stamatis-mavitzis/Power-Amplifier/Images/PXL_20261008_083058387.jpg

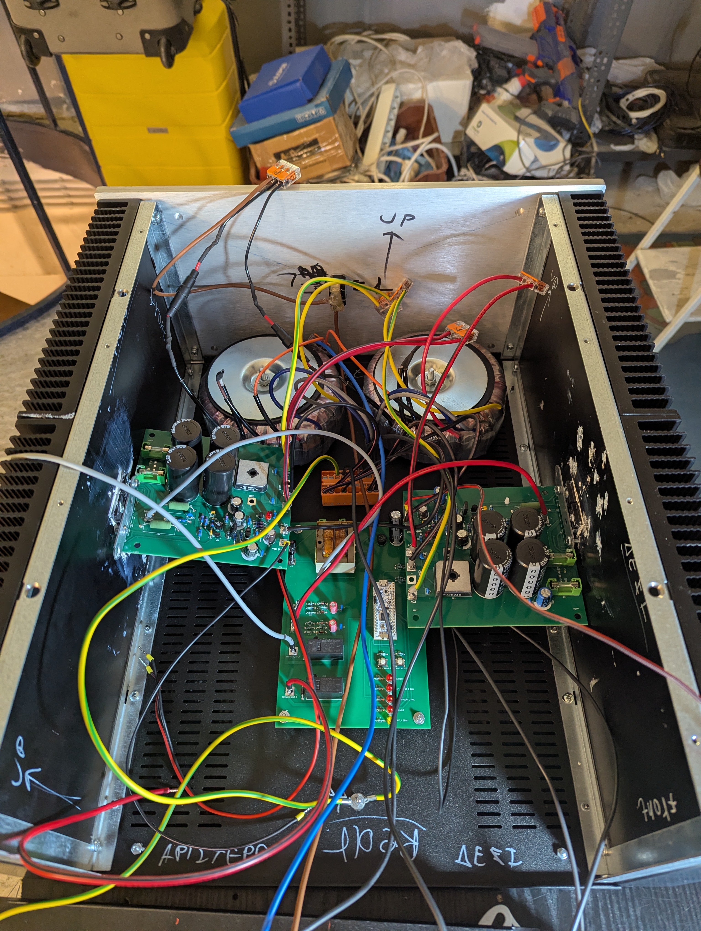
Images/PXL_20261008_083058387.jpg
