stamatis-mavitzis/Power-Amplifier/Images/PXL_20261008_091854718.jpg

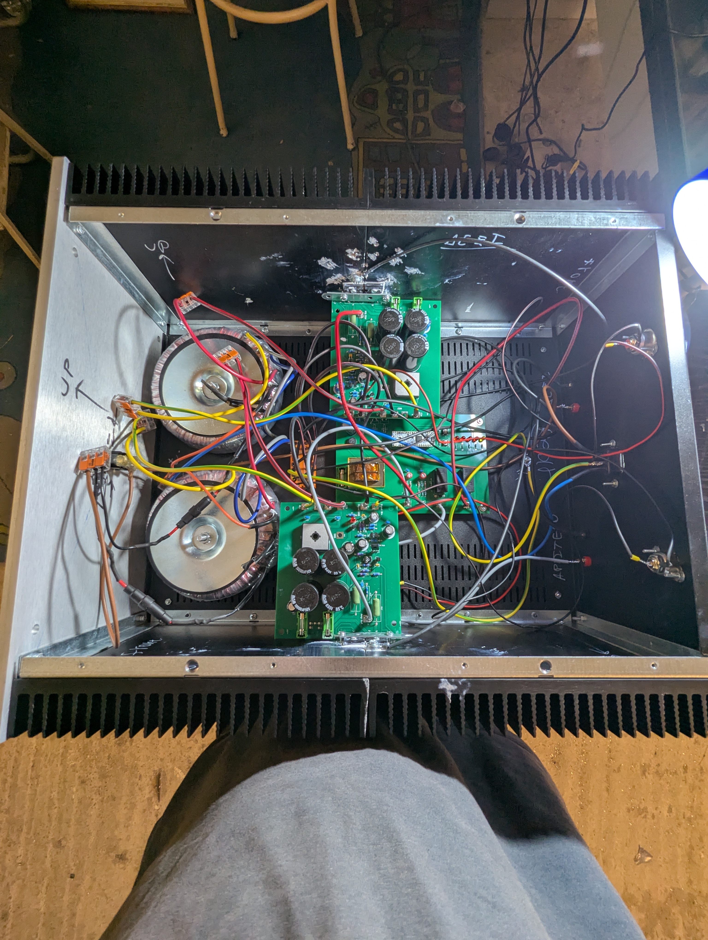
Images/PXL_20261008_091854718.jpg
