stamatis-mavitzis/Power-Amplifier/Images/PXL_20261008_150706582.jpg

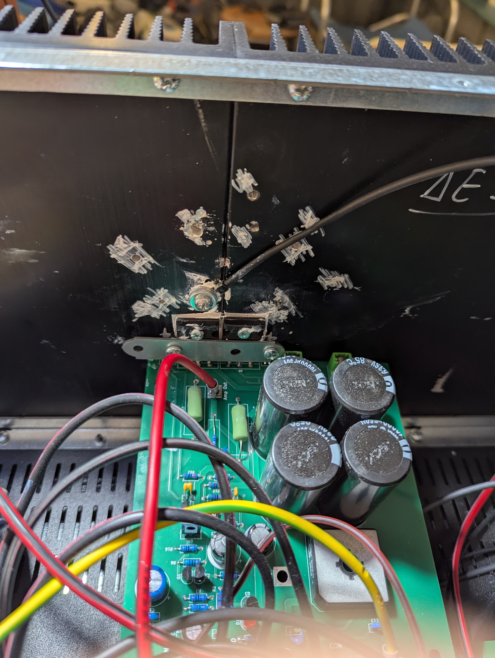
Images/PXL_20261008_150706582.jpg
