stamatis-mavitzis/Power-Amplifier/Images/PXL_20261008_164403830.jpg

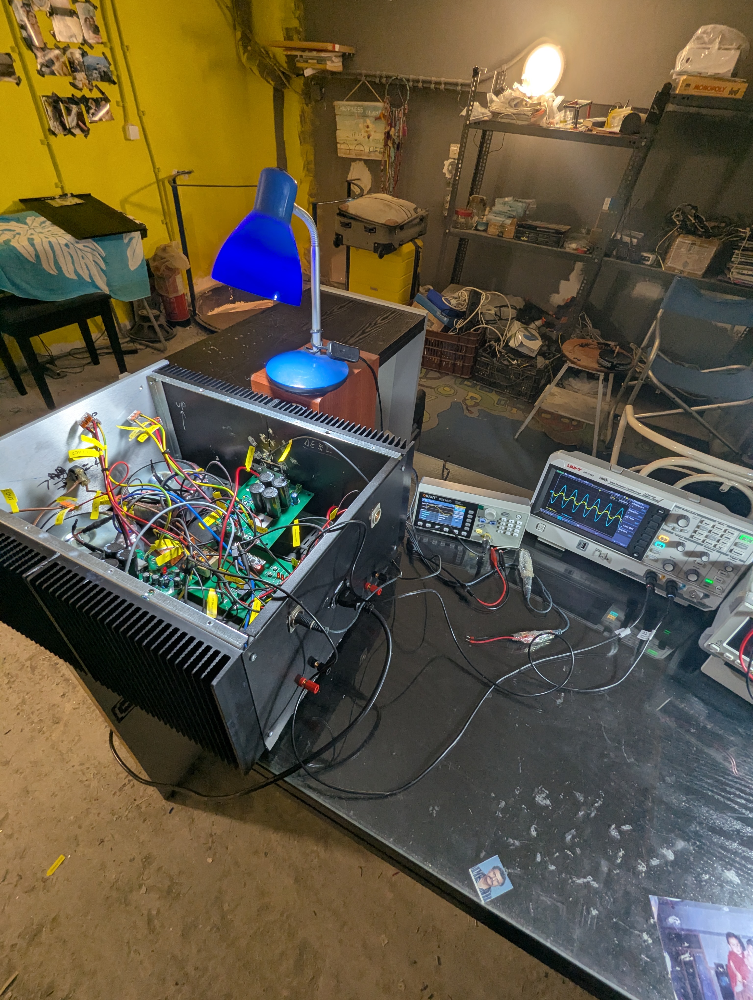
Images/PXL_20261008_164403830.jpg
